joaomachado23/7_PFC_Boost_Converter_V2/Testes & Resultados -Prints/inputCurrent_semCont0.png

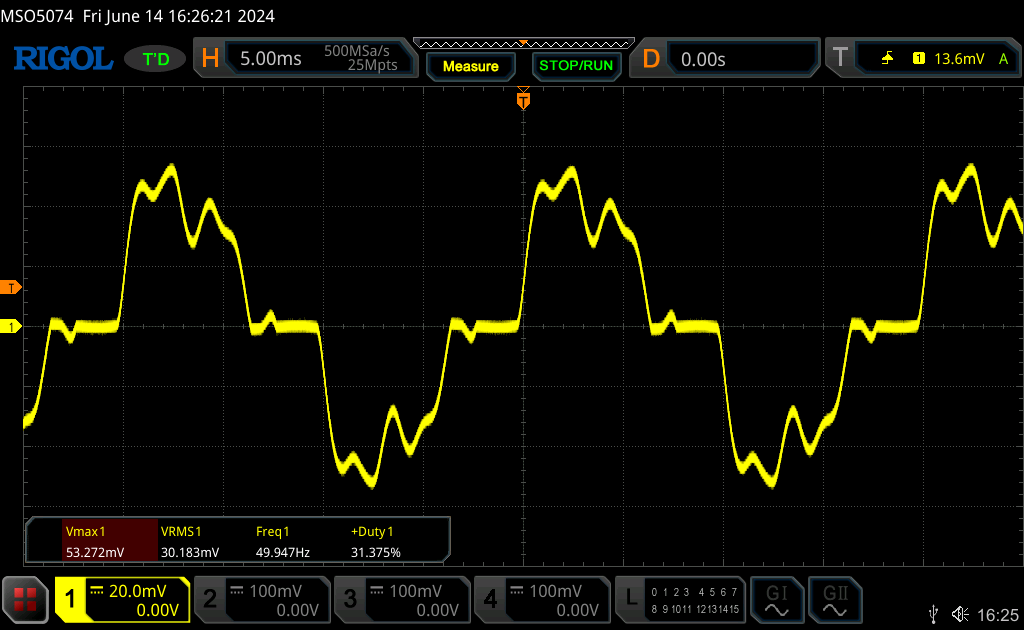
Testes & Resultados -Prints/inputCurrent_semCont0.png
