joaomachado23/7_PFC_Boost_Converter_V2/Testes & Resultados -Prints/pwm0.35.png

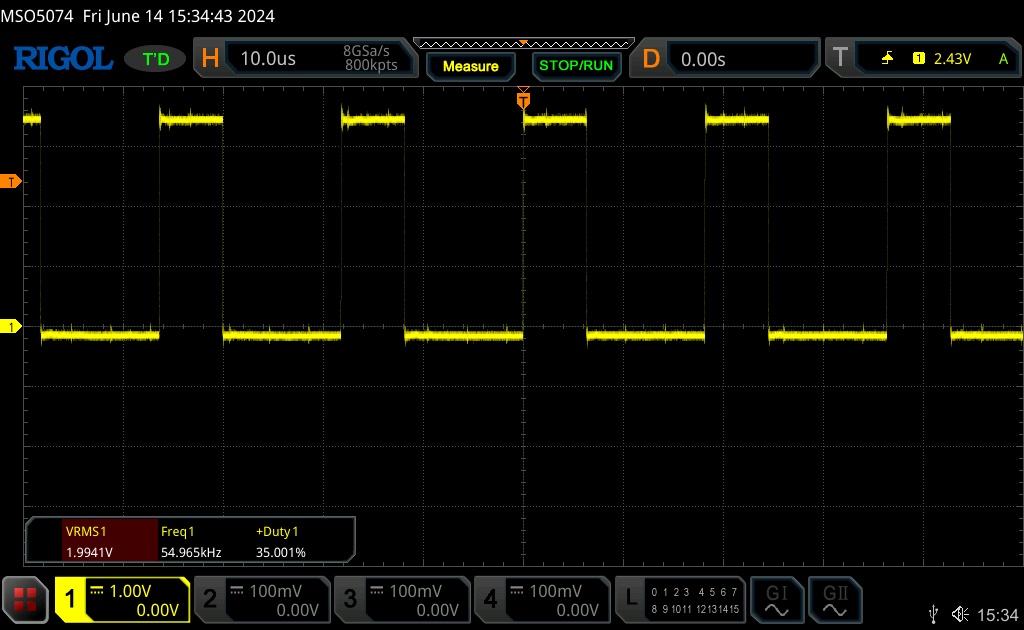
Testes & Resultados -Prints/pwm0.35.png
