joaomachado23/7_PFC_Boost_Converter_V2/Testes & Resultados -Prints/RigolDS1.png

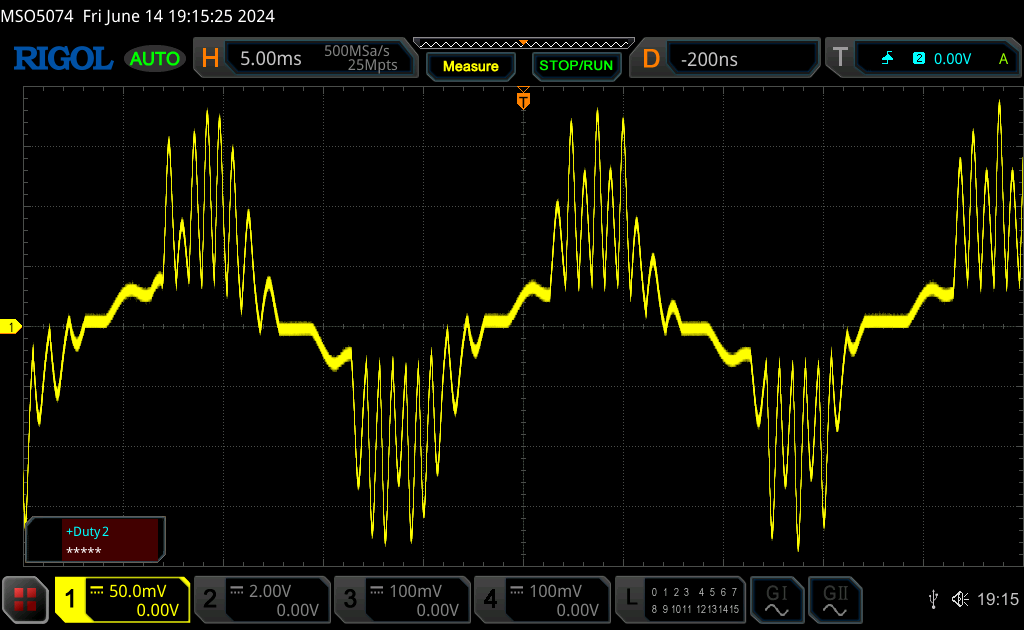
Testes & Resultados -Prints/RigolDS1.png
