joaomachado23/7_PFC_Boost_Converter_V2/Testes & Resultados -Prints/RigolDS6.png

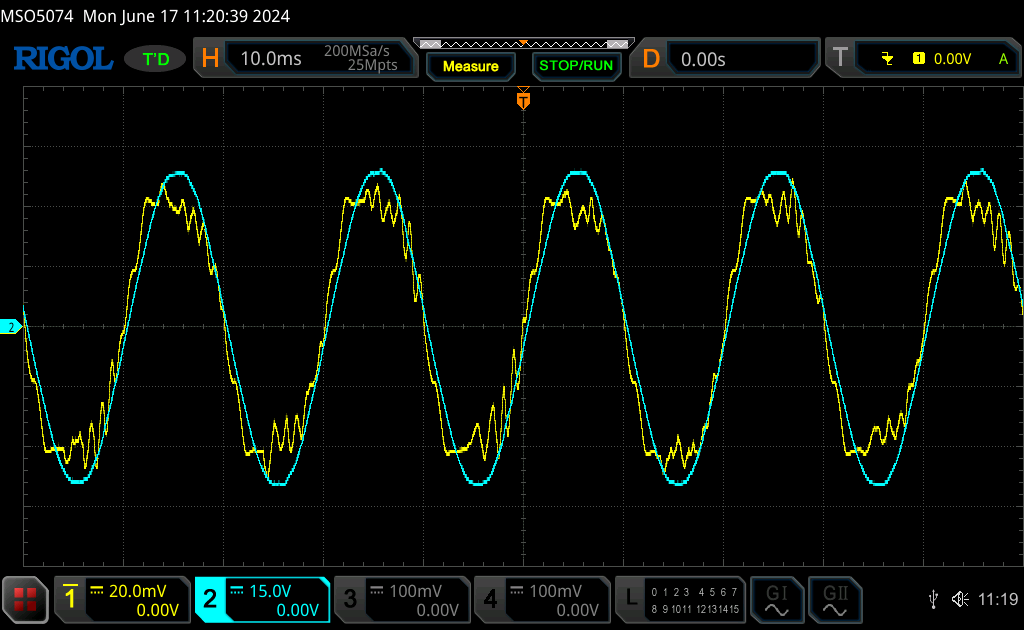
Testes & Resultados -Prints/RigolDS6.png
